qberry-io/qberryduino-gateway-one/src/qberryduino_one/Parsing.cpp

//  Copyright (c) 2018-present, Deniz Kanmaz. All rights reserved.
//  This source code is licensed under the GNU GENERAL PUBLIC
//  LICENCE V3. Use of this source code is governed by a license
//  that can be found in the LICENSE file.

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
//  E-mail: denizkanmaz@gmail.com

//  Description: Please refer to "Parsing.h".

/////////
// TODO: Refactor all the class.
/////////

#include "Arduino.h"
#include "Parsing.h"

// Returns whether the given index includes data we interest.
boolean Parsing::isInCGNSSIndexes(byte lineIndex) {
  return lineIndex == 1 // Fix Status
         || lineIndex == 3 // Latitude
         || lineIndex == 4 // Longtitude
         || lineIndex == 5 // MSL Altitude
         || lineIndex == 6 // Speed Over Ground
         || lineIndex == 7 // Course Over Ground
         || lineIndex == 8 // Fix Mode
         || lineIndex == 15 // GNSS Satellites Used
         || lineIndex == 16; // GLONASS Satellites in View
}

// Returns whether the given index includes data we interest.
boolean Parsing::isInBattIndexes(byte lineIndex) {
  return
    lineIndex == 0 // Charge Status
    || lineIndex == 1 // Battery Level (%)
    || lineIndex == 2; // Battery Voltage (mV)
}

// Clears the temprorary values.
void Parsing::clear() {
  for (int i = 0; i < LINES_LENGTH; i++) {
    s[i] = "";
  }
}

// Parses given Raw CBC response taken from the module.
String* Parsing::parseBatt(char * rawBattData) {

  clear();

  actualLineIndex = 0;
  lineIndex = 0;
  rawCharIndex = 0;

  for (rawCharIndex = 0;
       rawCharIndex < String(rawBattData).length();
       rawCharIndex++) {

    if (rawBattData[rawCharIndex] == SEPERATOR
        || (rawBattData[rawCharIndex] == 'O'
            && rawBattData[rawCharIndex + 1] == 'K')) {

      if (isInBattIndexes(lineIndex)) {
        actualLineIndex++;
      }

      lineIndex++;
      continue;
    }

    if (isInBattIndexes(lineIndex)) {
      if (lineIndex == 0) {
        Serial.println(String(rawBattData[rawCharIndex]));
        if (rawCharIndex == 6) {
          s[actualLineIndex] += String(rawBattData[rawCharIndex]);
        }
      } else {
        s[actualLineIndex] += String(rawBattData[rawCharIndex]);
      }
    }
  }
  return s;
}

// Parses given Raw CGNSINF response taken from the module.
// NOTICE: The raw message must be in "RMC" sequence.
String* Parsing::parseNMEAData(char* rawNMEAData) {

  clear();

  actualLineIndex = 0;
  lineIndex = 0;
  rawCharIndex = 0;

  for (rawCharIndex = 0;
       rawCharIndex < String(rawNMEAData).length();
       rawCharIndex++) {

    if (rawNMEAData[rawCharIndex] == SEPERATOR) {
      if (isInCGNSSIndexes(lineIndex)) {
        actualLineIndex++;
      }

      lineIndex++;
      continue;
    }

    if (isInCGNSSIndexes(lineIndex)) {
      s[actualLineIndex] += String(rawNMEAData[rawCharIndex]);
    }
  }

  return s;
}
